kevinrigot/ShellyRemote/schema/20220103_230530.jpg

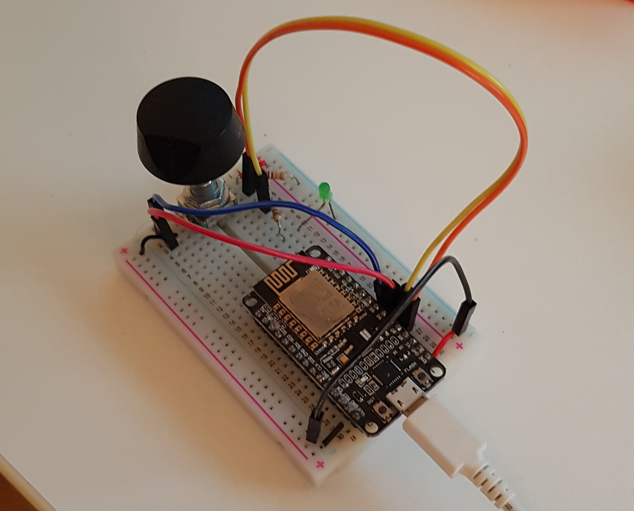
schema/20220103_230530.jpg
